teuler/Grundig60/pictures/DAB_Radio_v2_Leiterplatte.png

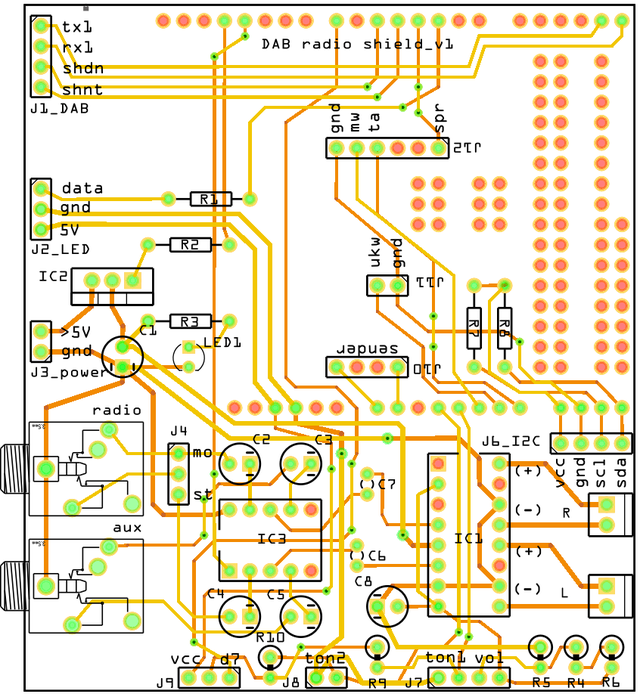
pictures/DAB_Radio_v2_Leiterplatte.png
