teuler/Grundig60/pictures/DAB_Radio_v2_Steckplatine.png

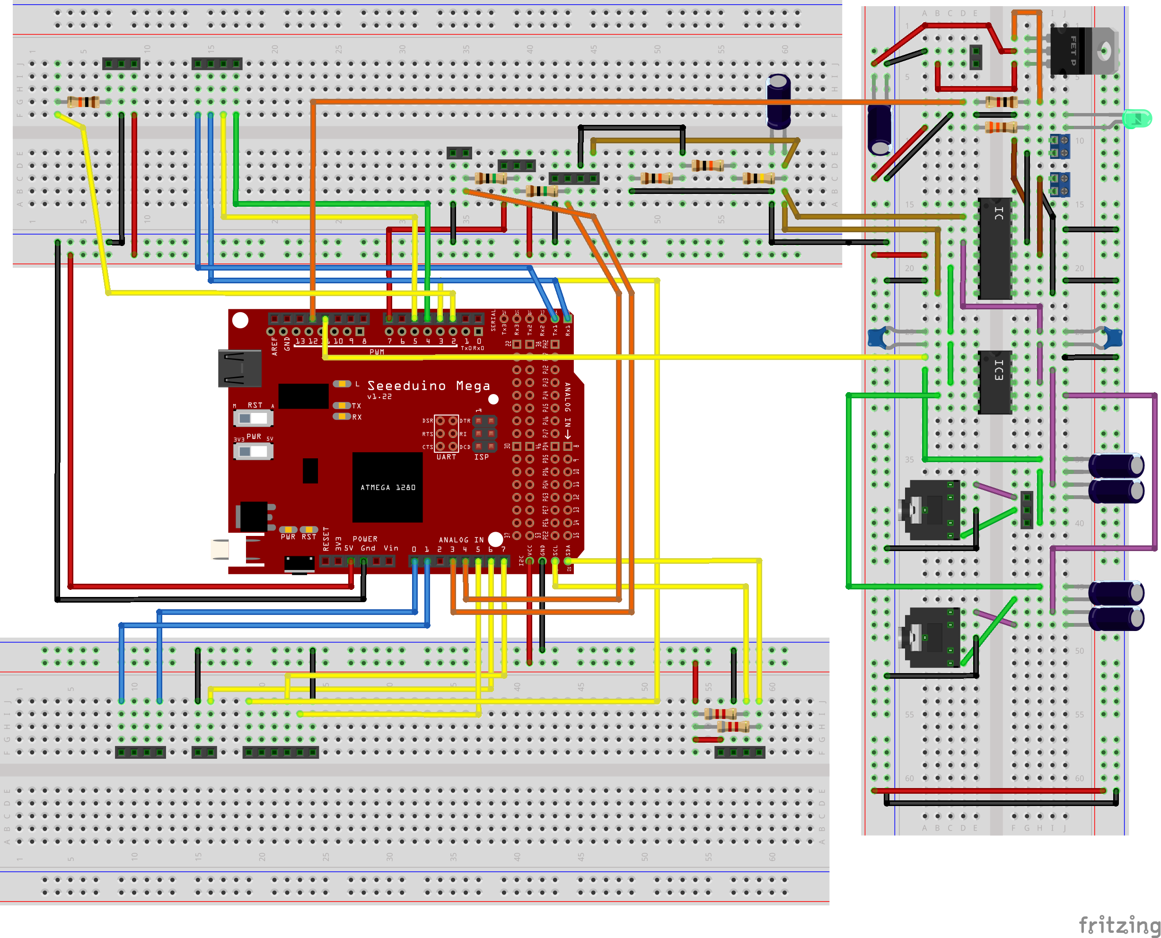
pictures/DAB_Radio_v2_Steckplatine.png
