teuler/Grundig60/pictures/pic001.jpg

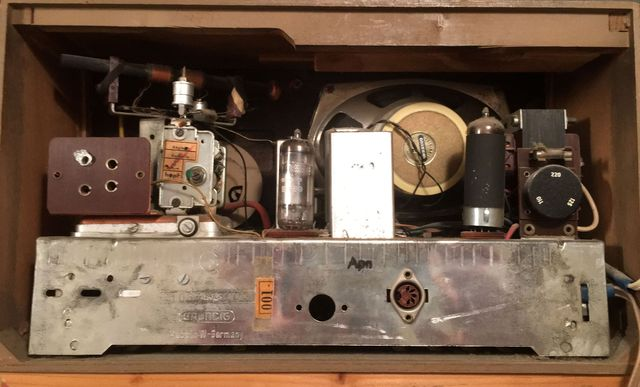
pictures/pic001.jpg
