teuler/Grundig60/pictures/pic002.jpg

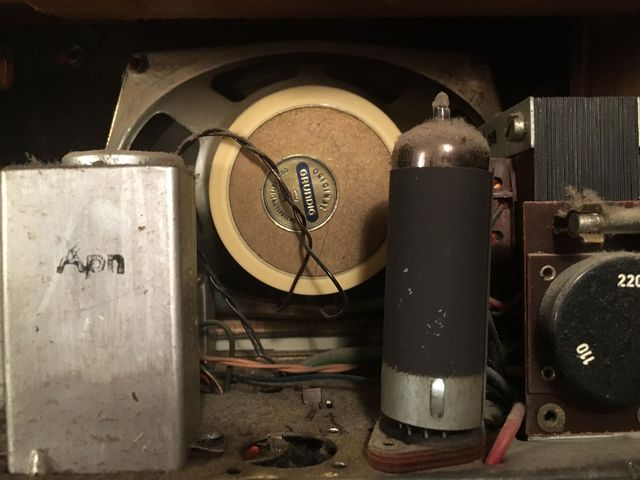
pictures/pic002.jpg
