teuler/Grundig60/pictures/pic003.jpg

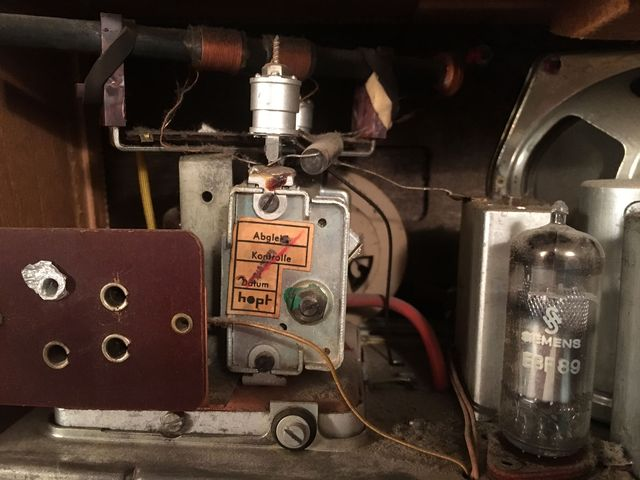
pictures/pic003.jpg
