teuler/Grundig60/pictures/pic004.jpg

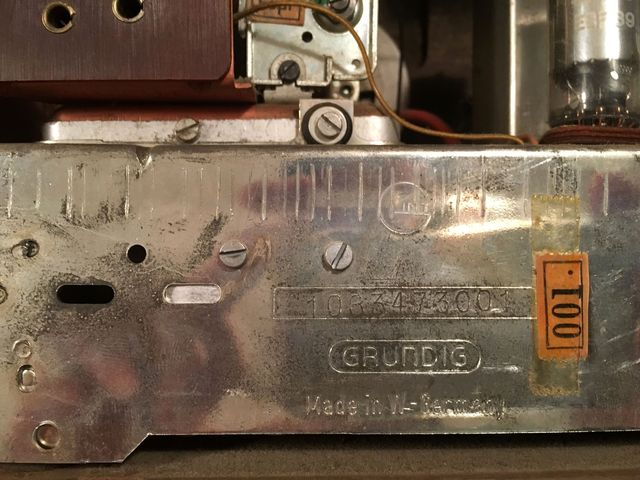
pictures/pic004.jpg
