teuler/Grundig60/pictures/pic005.jpg

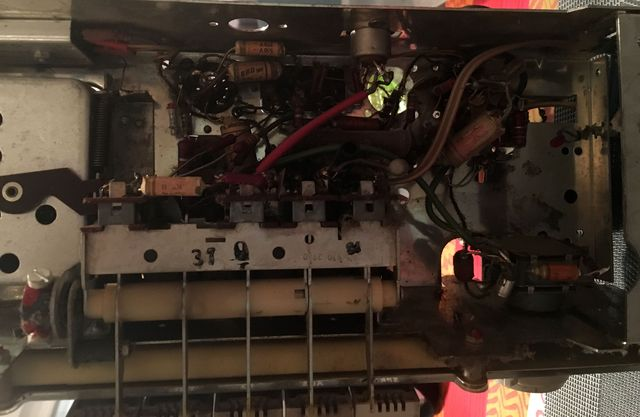
pictures/pic005.jpg
