teuler/Grundig60/pictures/pic006.jpg

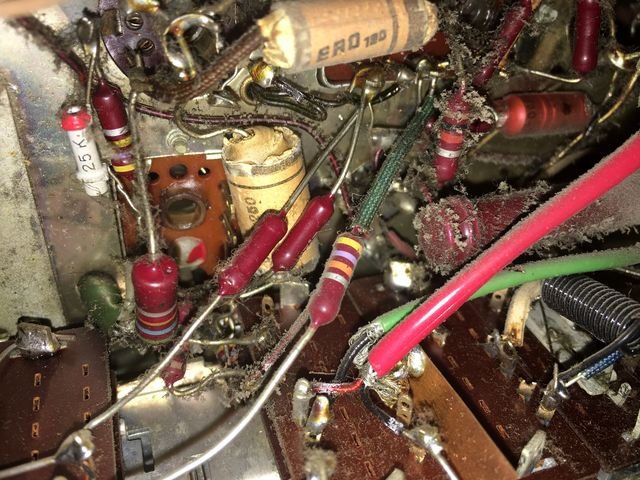
pictures/pic006.jpg
