teuler/Grundig60/pictures/pic007.jpg

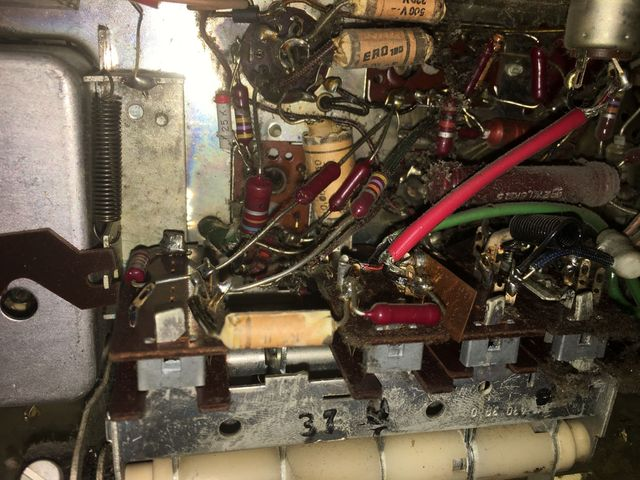
pictures/pic007.jpg
