teuler/Grundig60/pictures/pic008.jpg

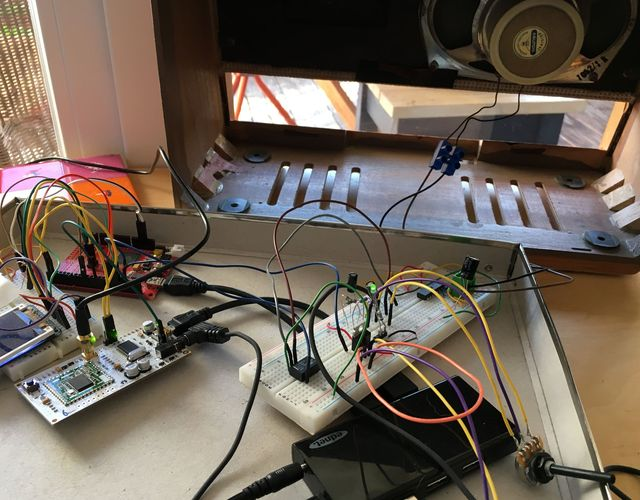
pictures/pic008.jpg
