teuler/Grundig60/pictures/pic009.jpg

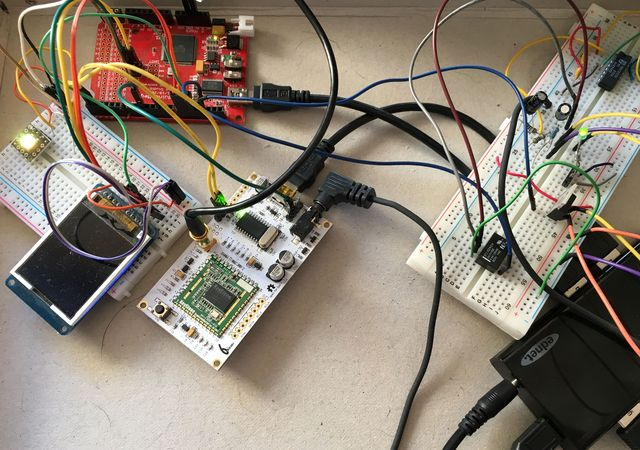
pictures/pic009.jpg
