teuler/Grundig60/pictures/pic010.jpg

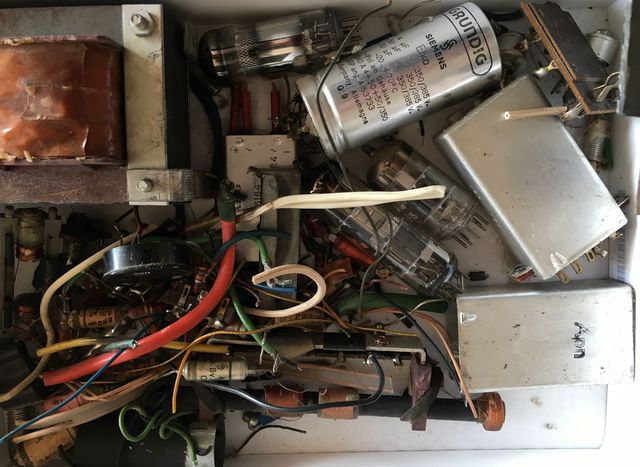
pictures/pic010.jpg
