teuler/Grundig60/pictures/pic012.jpg

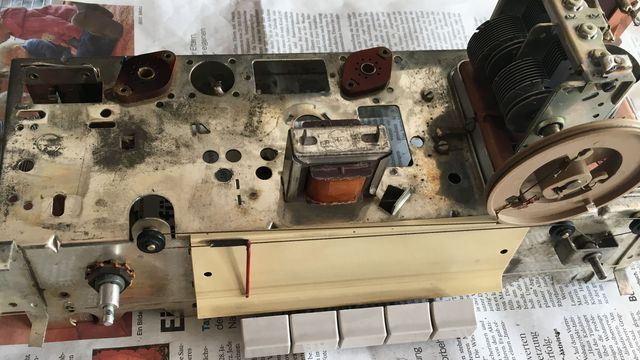
pictures/pic012.jpg
