teuler/Grundig60/pictures/pic013.jpg

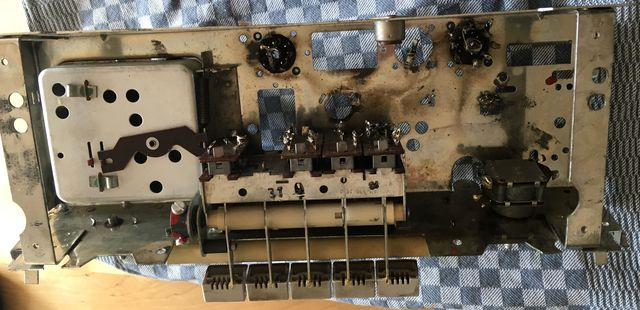
pictures/pic013.jpg
