teuler/Grundig60/pictures/pic014.jpg

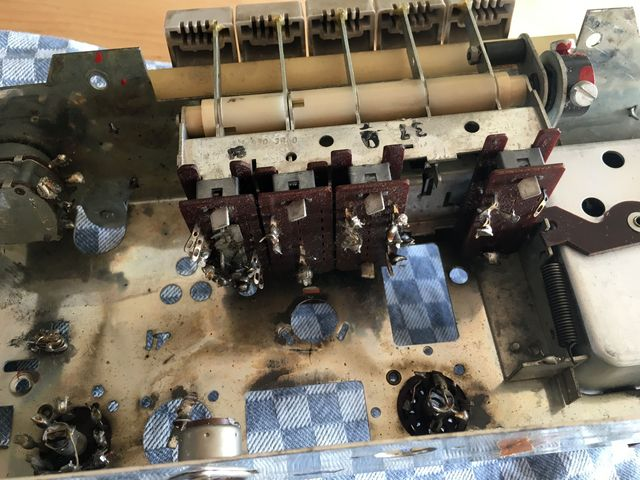
pictures/pic014.jpg
