teuler/Grundig60/pictures/pic015.jpg

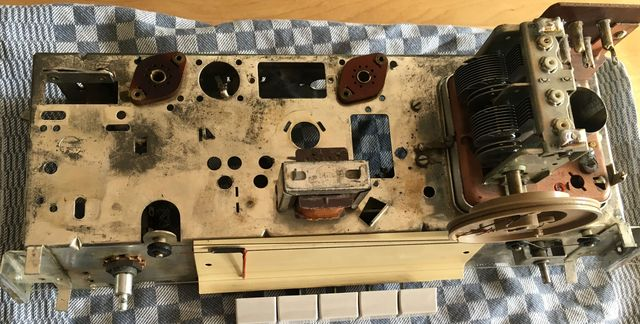
pictures/pic015.jpg
