teuler/Grundig60/pictures/pic016.jpg

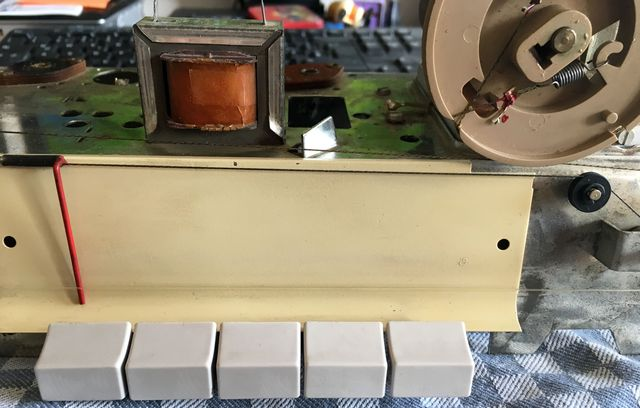
pictures/pic016.jpg
