teuler/Grundig60/pictures/pic017.jpg

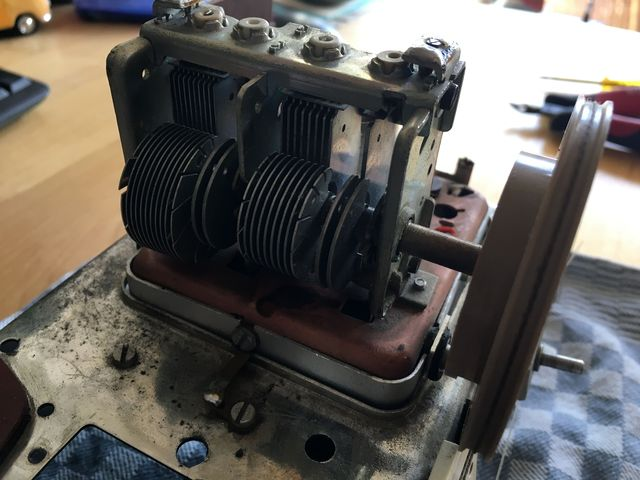
pictures/pic017.jpg
