teuler/Grundig60/pictures/pic018.jpg

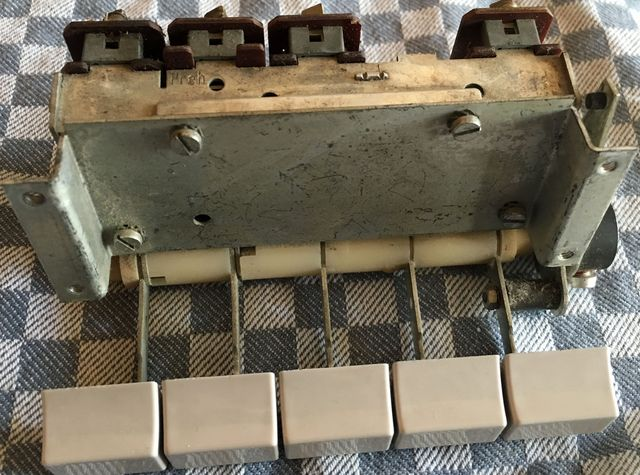
pictures/pic018.jpg
