teuler/Grundig60/pictures/pic019.jpg

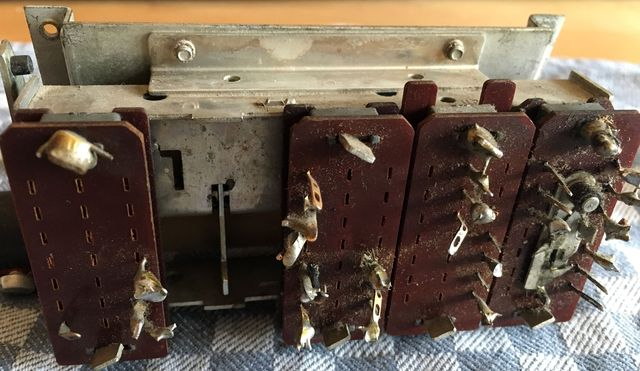
pictures/pic019.jpg
