teuler/Grundig60/pictures/pic020.jpg

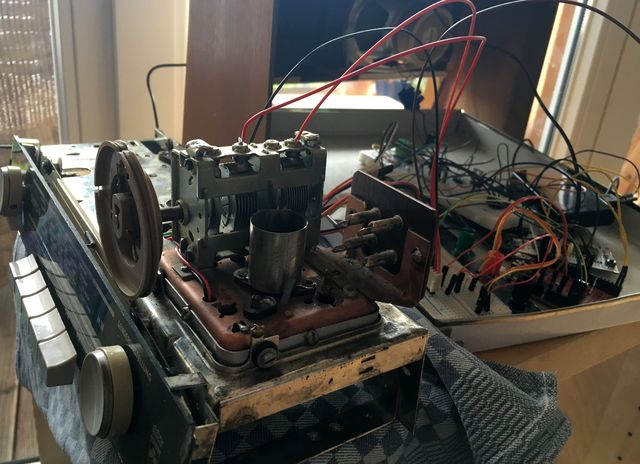
pictures/pic020.jpg
