teuler/Grundig60/pictures/pic022.jpg

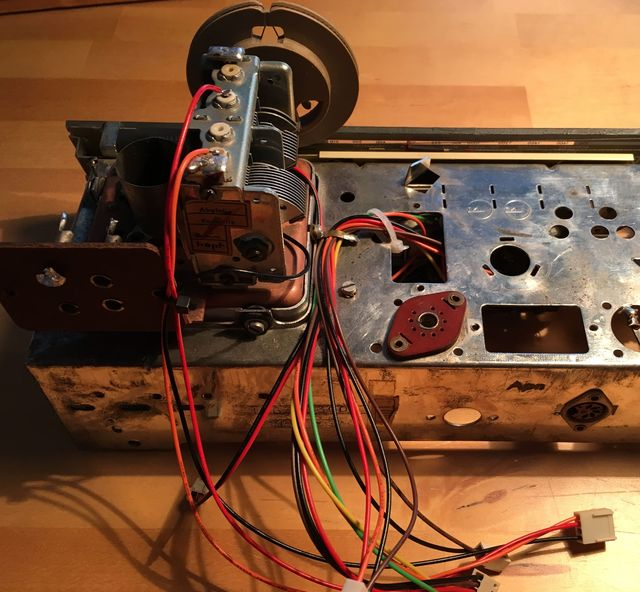
pictures/pic022.jpg
