teuler/Grundig60/pictures/pic023.jpg

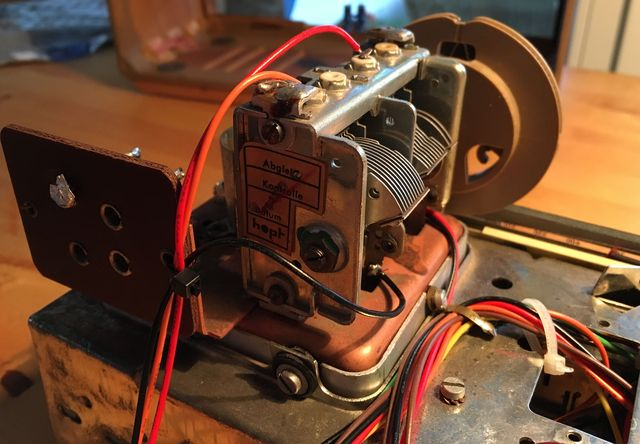
pictures/pic023.jpg
