teuler/Grundig60/pictures/pic024.jpg

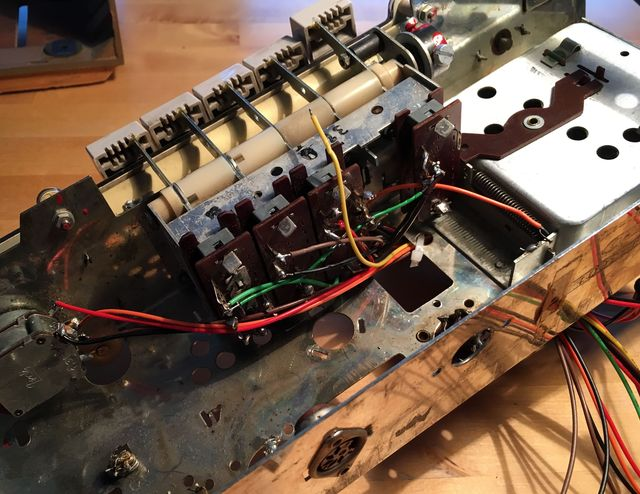
pictures/pic024.jpg
