teuler/Grundig60/pictures/pic025.jpg

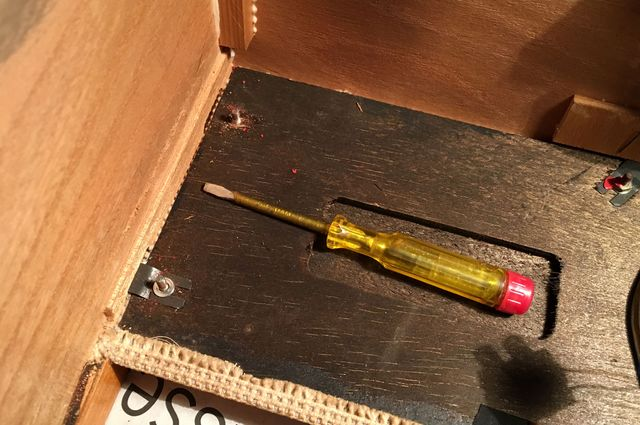
pictures/pic025.jpg
