teuler/Grundig60/pictures/pic026.jpg

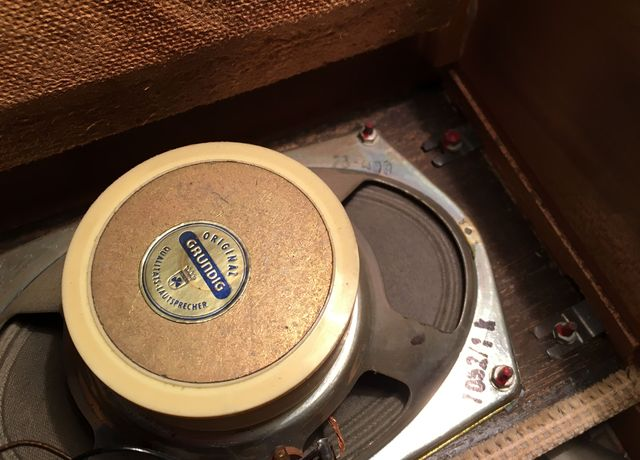
pictures/pic026.jpg
