teuler/Grundig60/pictures/pic027.jpg

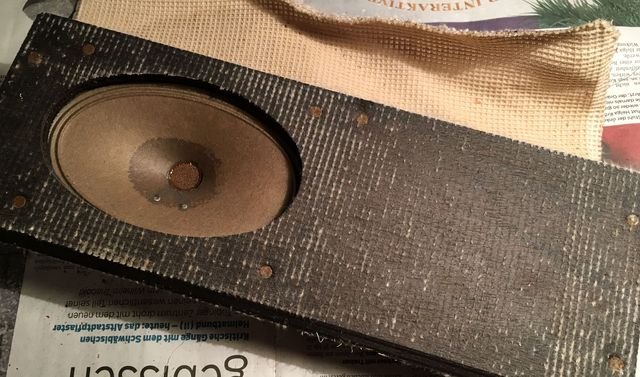
pictures/pic027.jpg
