teuler/Grundig60/pictures/pic029.jpg

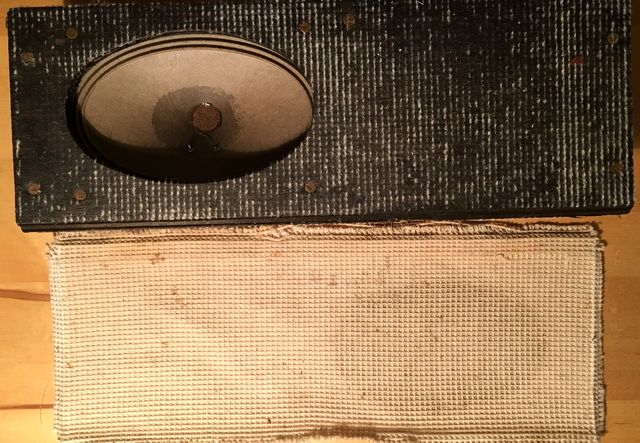
pictures/pic029.jpg
