teuler/Grundig60/pictures/pic030.jpg

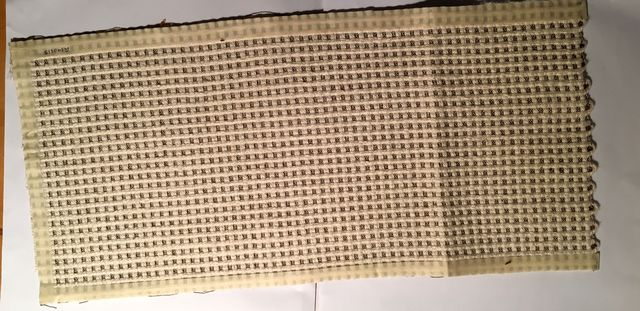
pictures/pic030.jpg
