teuler/Grundig60/pictures/pic031.jpg

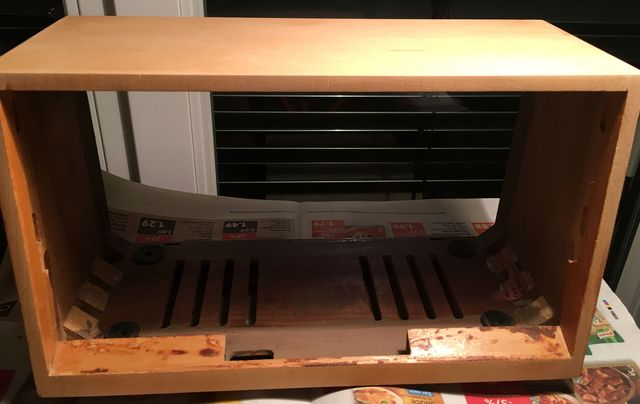
pictures/pic031.jpg
