teuler/Grundig60/pictures/pic032.jpg

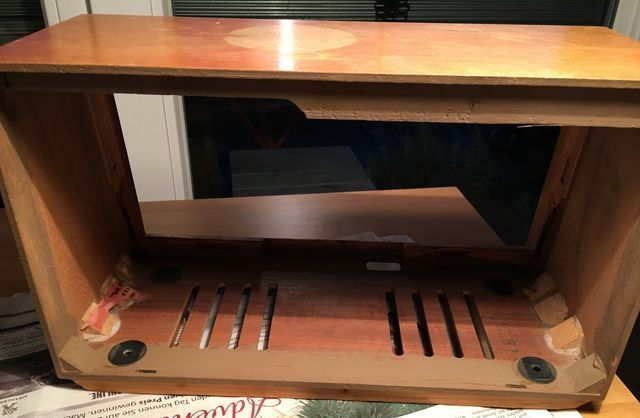
pictures/pic032.jpg
