teuler/Grundig60/pictures/pic033.jpg

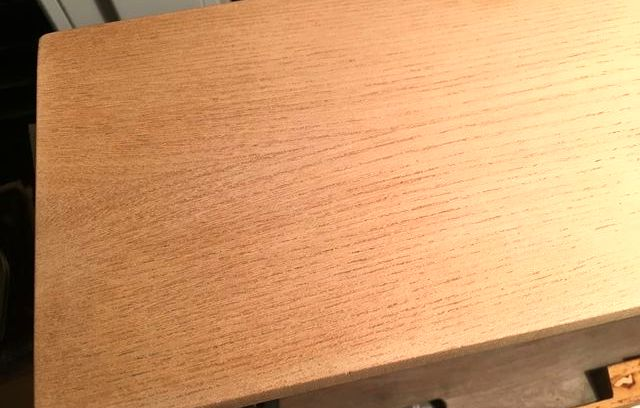
pictures/pic033.jpg
