teuler/Grundig60/pictures/pic034.jpg

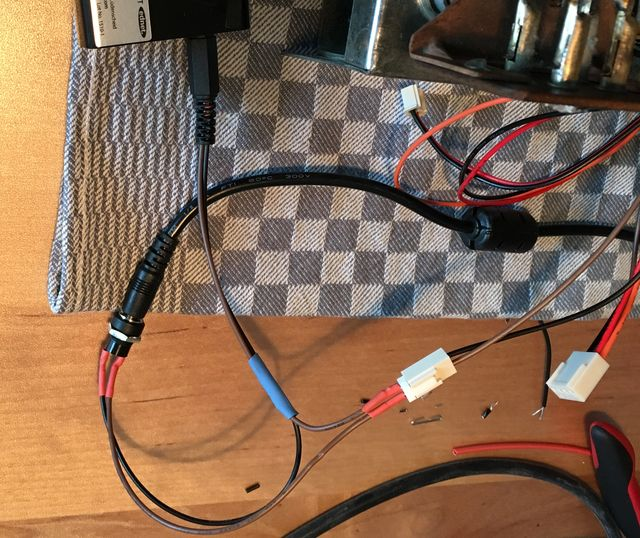
pictures/pic034.jpg
