teuler/Grundig60/pictures/pic035.jpg

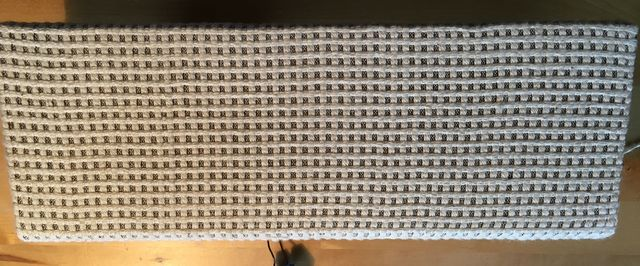
pictures/pic035.jpg
