teuler/Grundig60/pictures/pic036.jpg

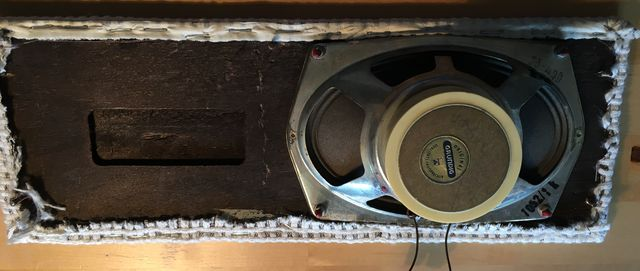
pictures/pic036.jpg
