teuler/Grundig60/pictures/pic037.jpg

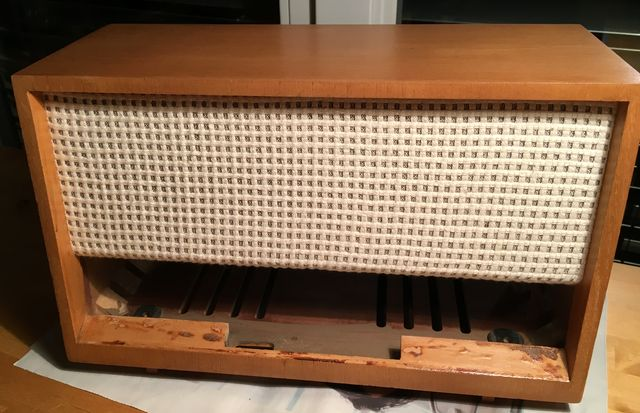
pictures/pic037.jpg
