teuler/Grundig60/pictures/pic038.jpg

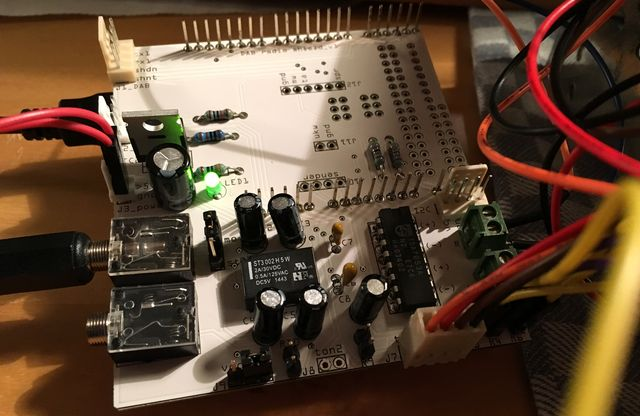
pictures/pic038.jpg
