teuler/Grundig60/pictures/pic039.jpg

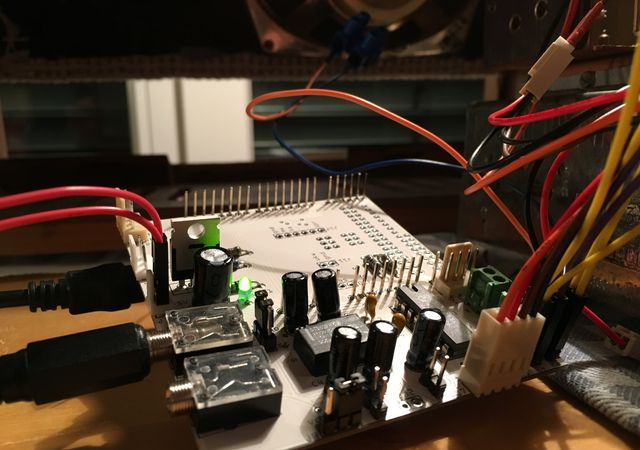
pictures/pic039.jpg
