teuler/Grundig60/pictures/pic040.jpg

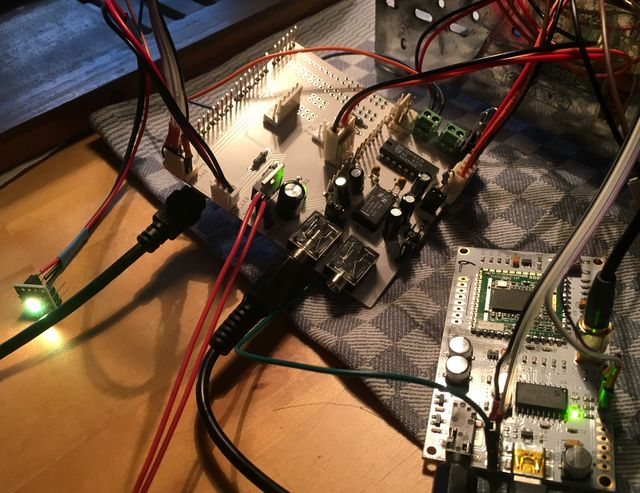
pictures/pic040.jpg
