teuler/Grundig60/pictures/pic042.jpg

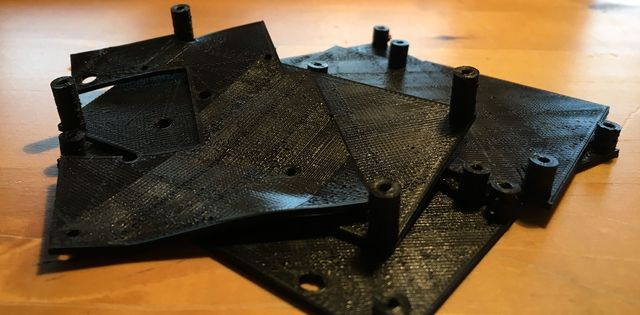
pictures/pic042.jpg
