teuler/Grundig60/pictures/pic043.jpg

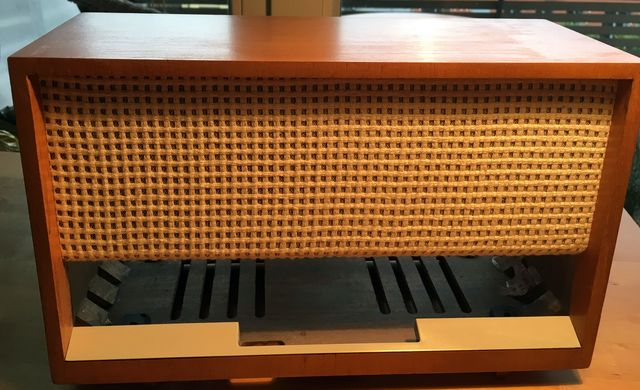
pictures/pic043.jpg
