teuler/Grundig60/pictures/pic044.jpg

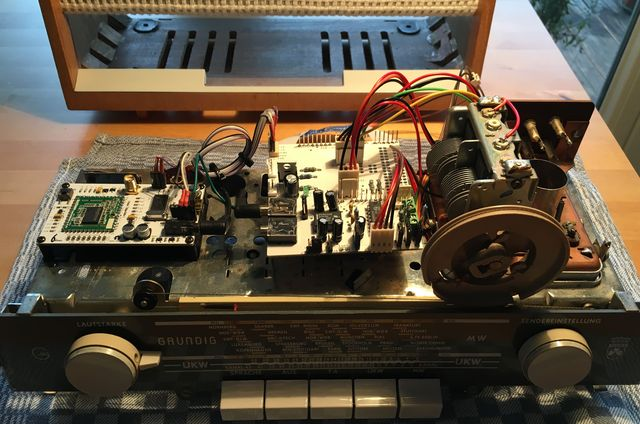
pictures/pic044.jpg
