teuler/Grundig60/pictures/pic045.jpg

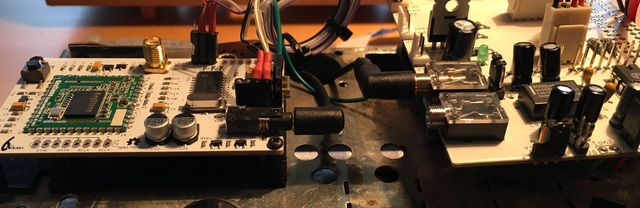
pictures/pic045.jpg
