teuler/Grundig60/pictures/pic046.jpg

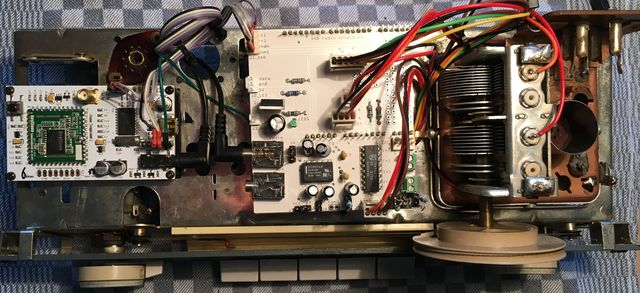
pictures/pic046.jpg
