teuler/Grundig60/pictures/pic047.jpg

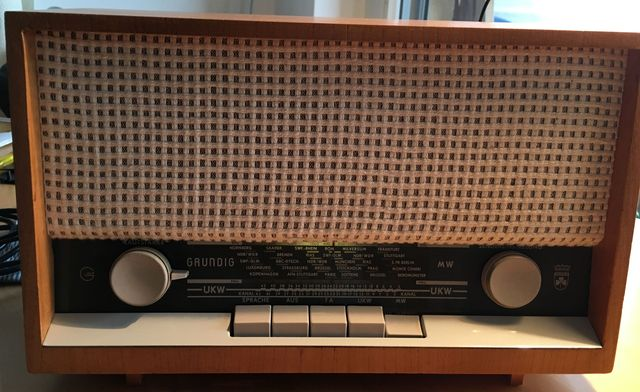
pictures/pic047.jpg
