teuler/Grundig60/pictures/pic048.jpg

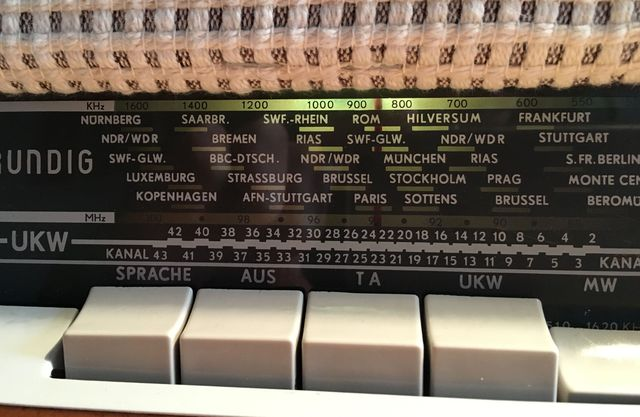
pictures/pic048.jpg
