teuler/Grundig60/pictures/pic049.jpg

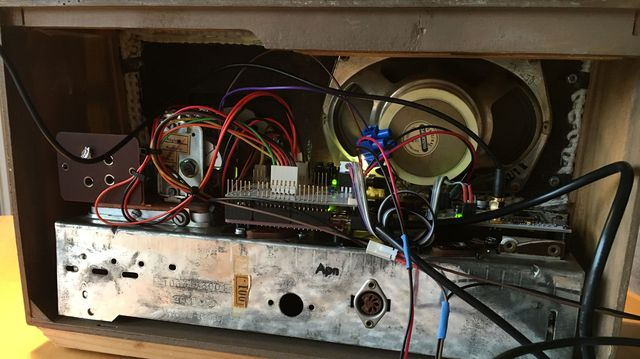
pictures/pic049.jpg
