teuler/Grundig60/pictures/pic050.jpg

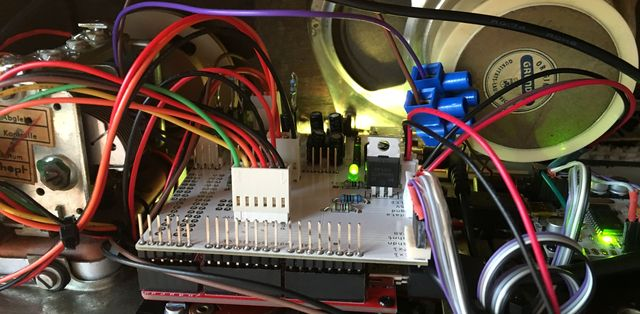
pictures/pic050.jpg
