teuler/Grundig60/pictures/pic051.jpg

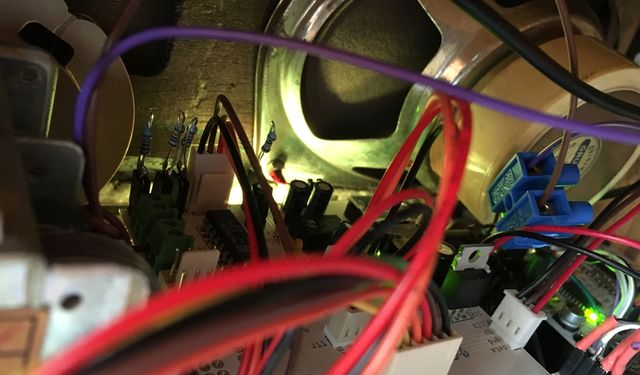
pictures/pic051.jpg
