teuler/Grundig60/pictures/pic052.jpg

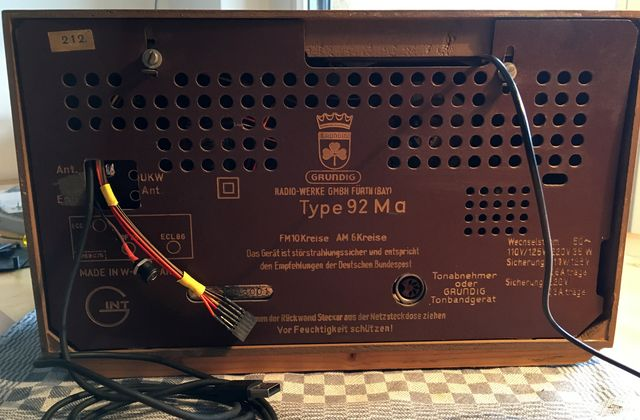
pictures/pic052.jpg
