teuler/Grundig60/pictures/pic053.jpg

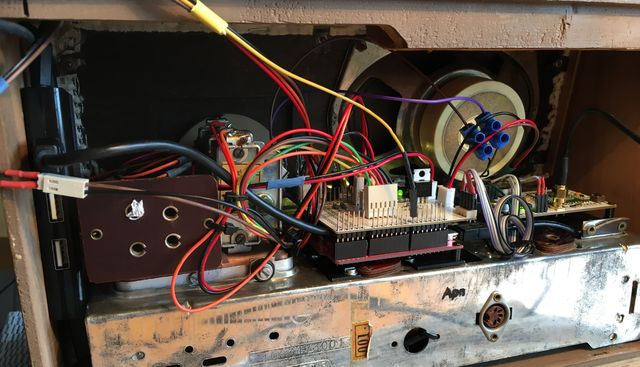
pictures/pic053.jpg
