teuler/Grundig60/pictures/pic054.jpg

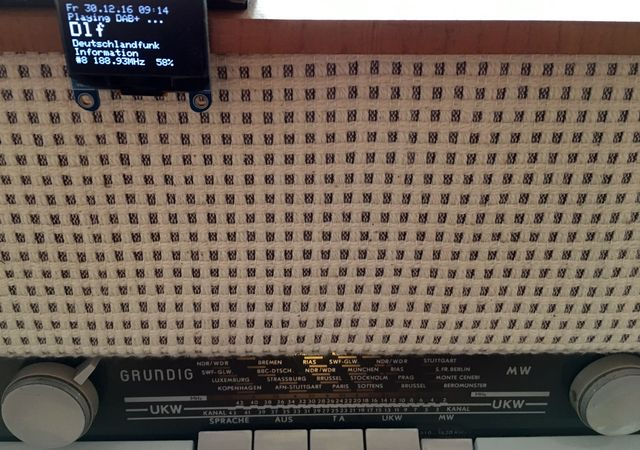
pictures/pic054.jpg
