teuler/Grundig60/pictures/pic055.jpg

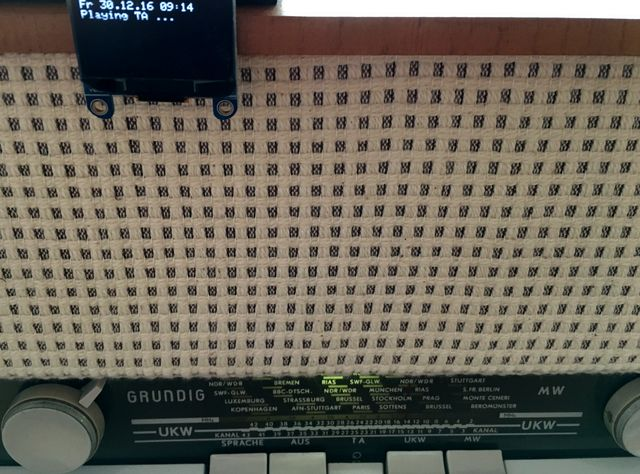
pictures/pic055.jpg
