teuler/Grundig60/pictures/Schema.png

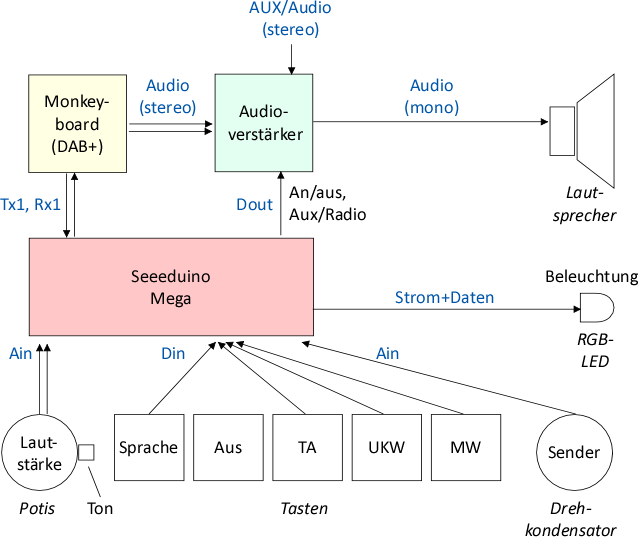
pictures/Schema.png
