teuler/Grundig60/pictures/Make02-17_S60.jpg

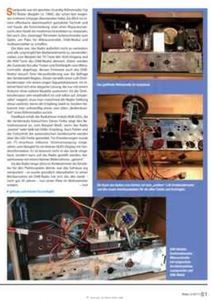
pictures/Make02-17_S60.jpg
